KCSAbeywickrama/Function-Generator/Enclosure/Renderings/1000uF_16V.JPG

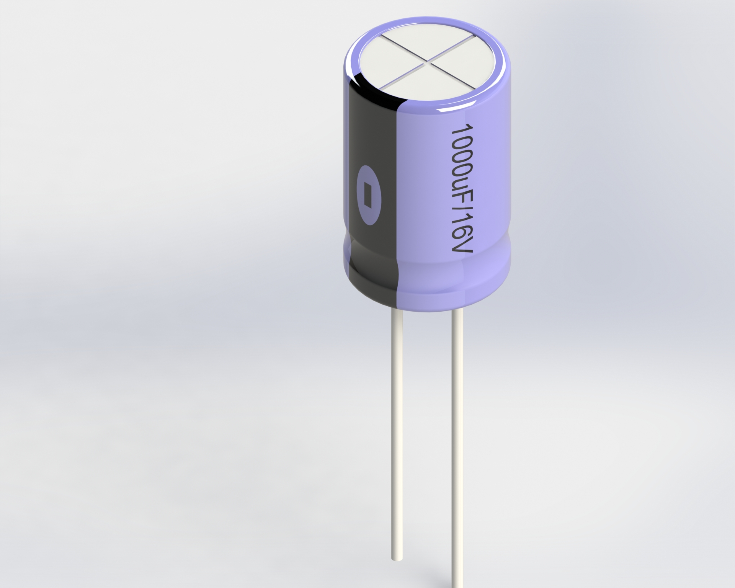
Enclosure/Renderings/1000uF_16V.JPG
