KCSAbeywickrama/Function-Generator/Enclosure/RV24AF-22-15R.png

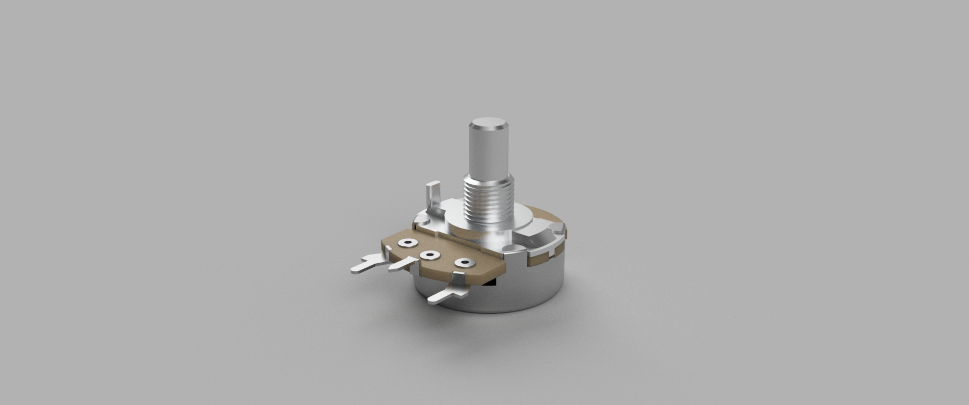
Enclosure/RV24AF-22-15R.png
