KCSAbeywickrama/Function-Generator/Enclosure/transformer/Transformer.step

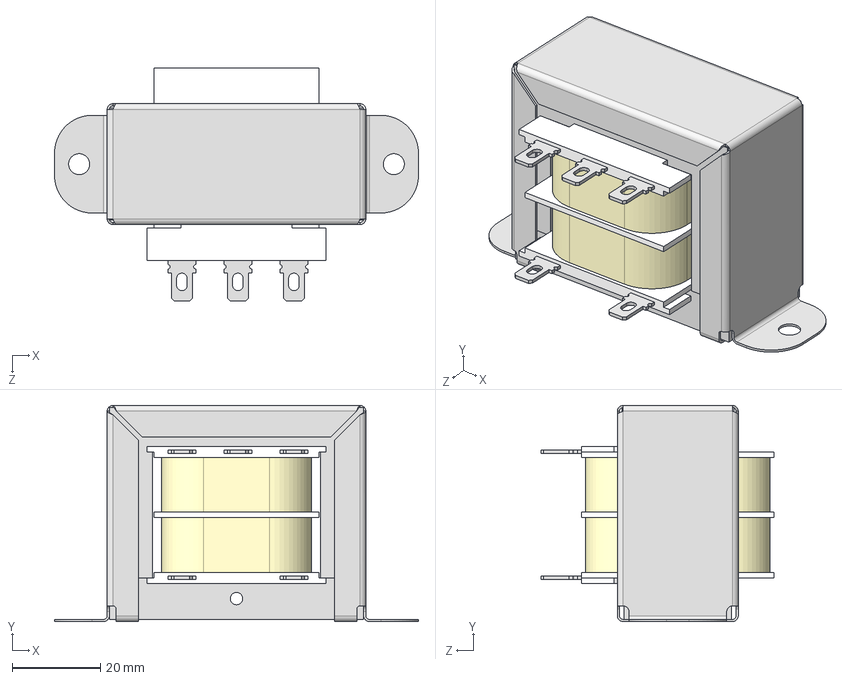
[picture p33: CAD file, 2022-11-06]
Enclosure/transformer/Transformer.step
82.6 x 49.0 x 52.9 mm
