KCSAbeywickrama/Function-Generator/Enclosure/spacer.SLDPRT

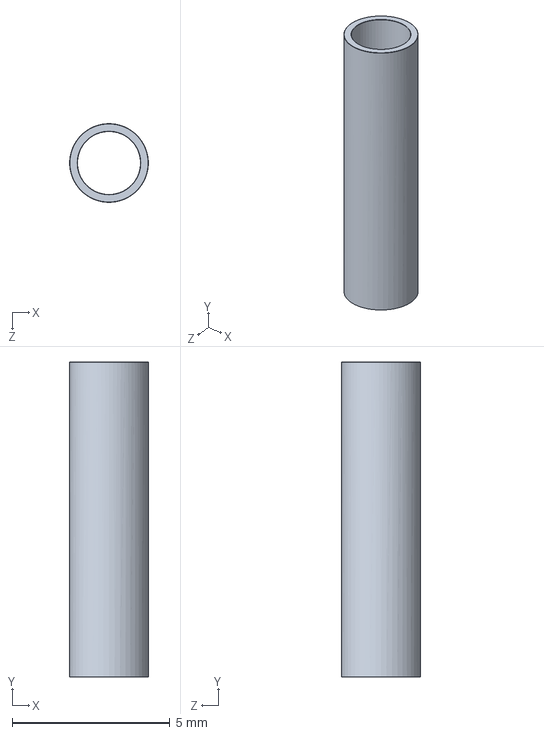
[picture p34: CAD file, 2022-11-06]
Enclosure/spacer.SLDPRT
2.50 x 10.0 x 2.50 mm
