KCSAbeywickrama/Function-Generator/Enclosure/probe_port.SLDPRT

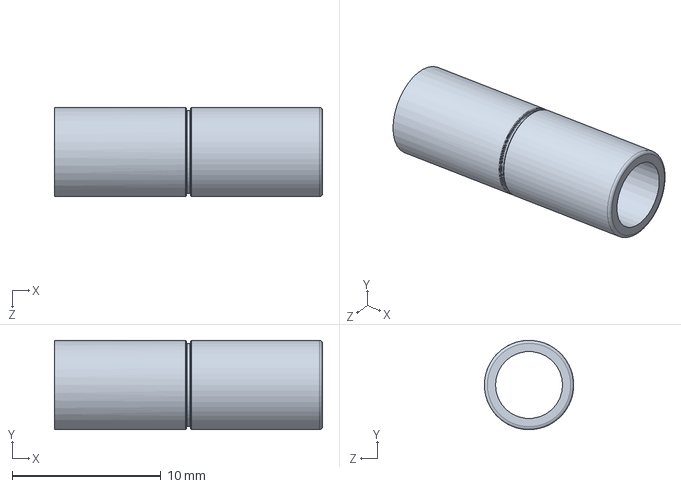
[picture p35: CAD file, 2022-11-06]
Enclosure/probe_port.SLDPRT
18.0 x 6.00 x 5.99 mm
