KCSAbeywickrama/Function-Generator/Enclosure/1000uF_16V.STEP

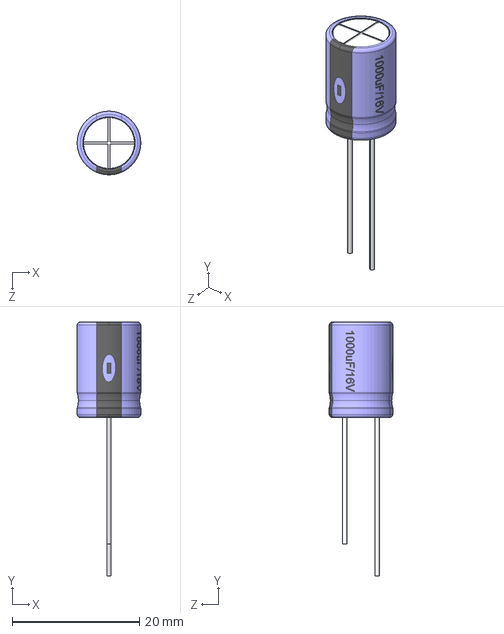
[picture p36: CAD file, 2022-11-06]
Enclosure/1000uF_16V.STEP
9.99 x 39.9 x 10.0 mm
