KCSAbeywickrama/Function-Generator/Enclosure/RV24AF-22-15R.step

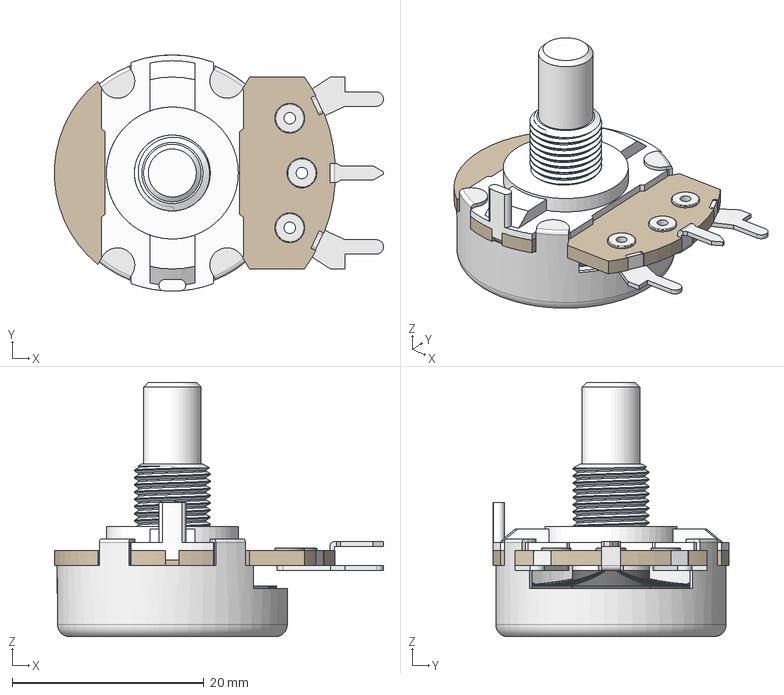
[picture p37: CAD file, 2022-11-06]
Enclosure/RV24AF-22-15R.step
34.3 x 24.6 x 26.5 mm
