KCSAbeywickrama/Function-Generator/Enclosure/knob_large.SLDPRT

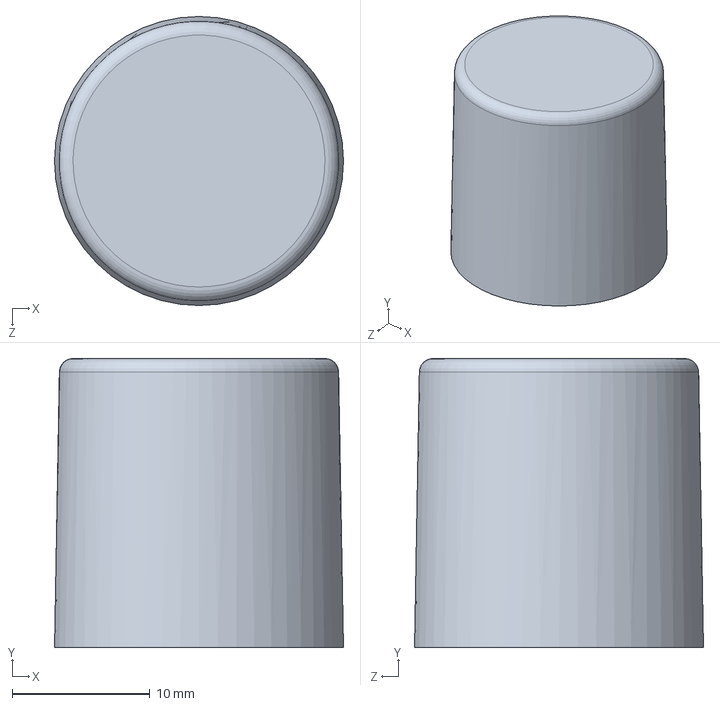
[picture p38: CAD file, 2022-11-06]
Enclosure/knob_large.SLDPRT
21.0 x 21.0 x 21.0 mm
