KCSAbeywickrama/Function-Generator/Enclosure/pwr_supply.SLDPRT

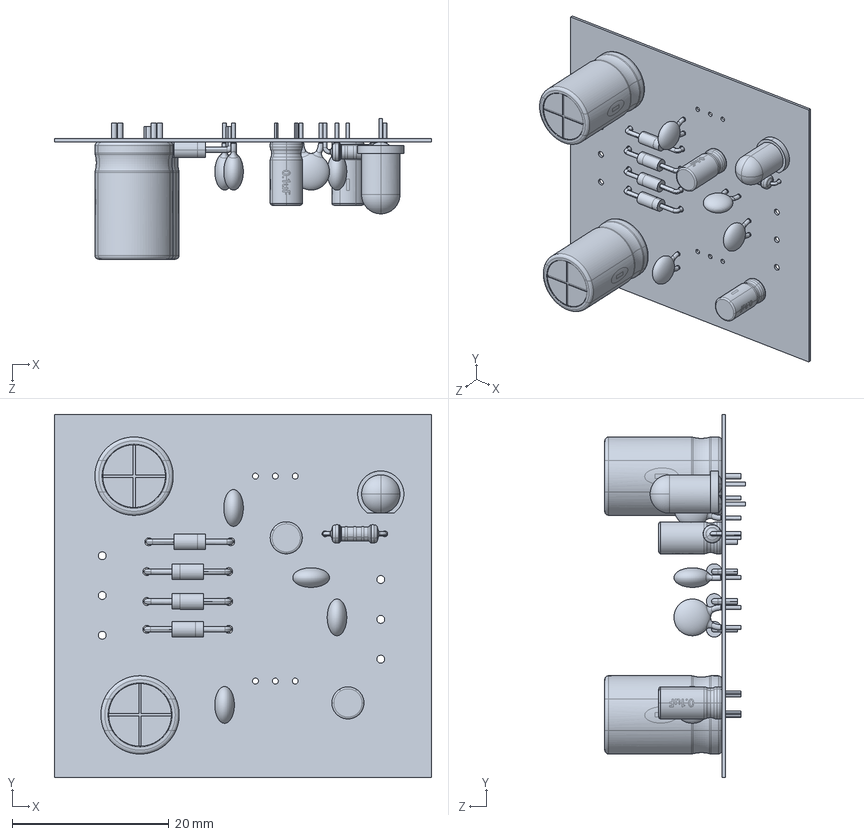
[picture p39: CAD file, 2022-11-06]
Enclosure/pwr_supply.SLDPRT
48.1 x 46.4 x 17.9 mm
