KCSAbeywickrama/Function-Generator/Enclosure/power switch.SLDPRT

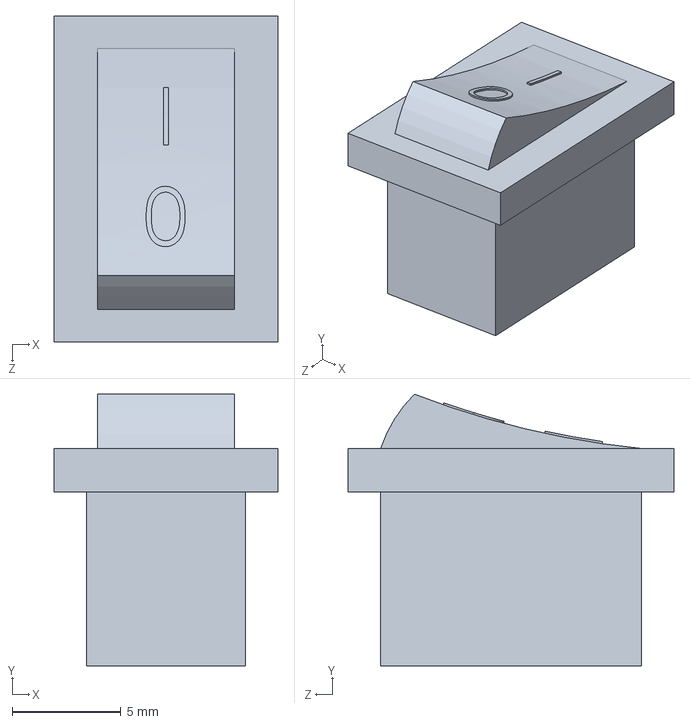
[picture p40: CAD file, 2022-11-06]
Enclosure/power switch.SLDPRT
10.3 x 12.5 x 15.0 mm
