KCSAbeywickrama/Function-Generator/PCB/Power_Supply_Project/PWR_supply_sch.step

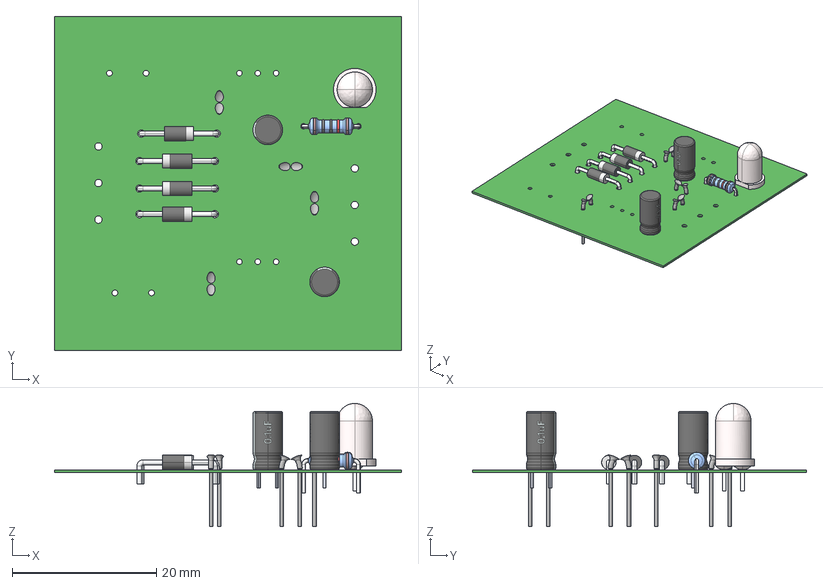
[picture p41: CAD file, 2022-11-06]
PCB/Power_Supply_Project/PWR_supply_sch.step
48.1 x 46.4 x 17.1 mm
Resistor_10K_Ohm_tol1pct_0,25W__07,62
0.1uF x 2
LED_5mm_white_TH
Diode_(1) x 4
10pF_Ceramic_Disc_2_RGB8421504 x 4
