KCSAbeywickrama/Function-Generator/Enclosure/POWER_SWITCH_1353.SLDPRT

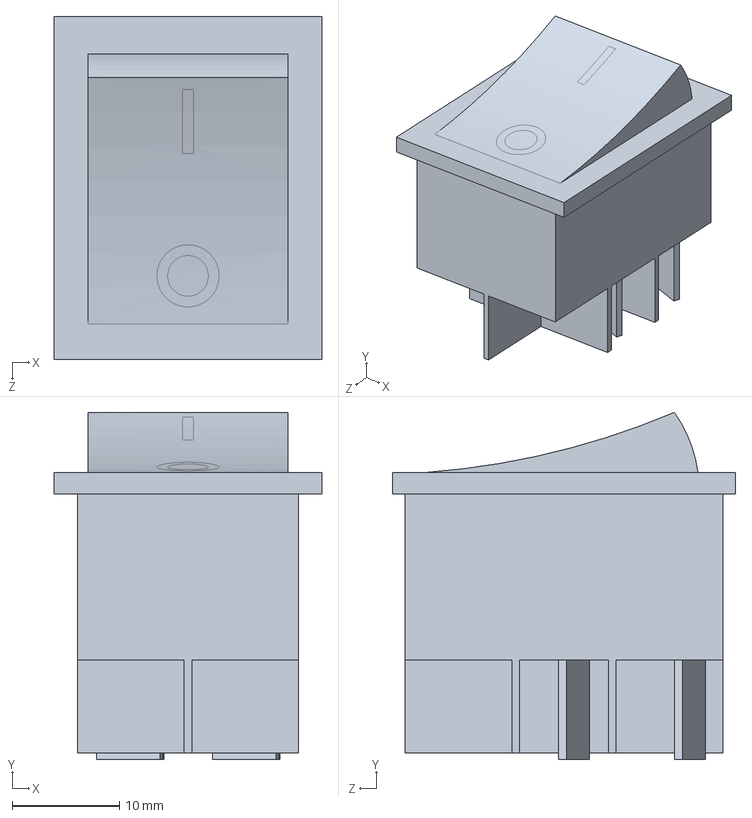
[picture p42: CAD file, 2022-11-06]
Enclosure/POWER_SWITCH_1353.SLDPRT
25.0 x 32.4 x 32.0 mm
