KCSAbeywickrama/Function-Generator/Enclosure/knob_small.SLDPRT

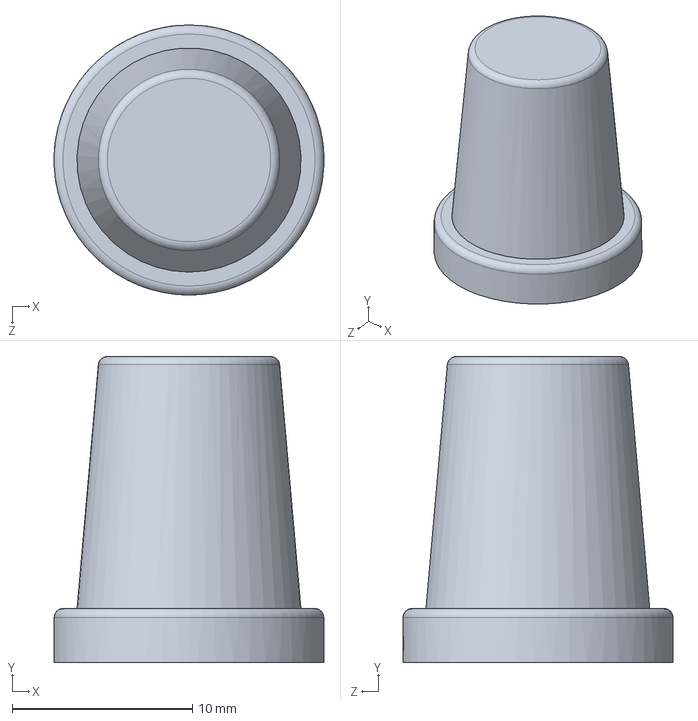
[picture p43: CAD file, 2022-11-06]
Enclosure/knob_small.SLDPRT
15.0 x 17.0 x 15.0 mm
