KCSAbeywickrama/Function-Generator/Prints/multisim.png

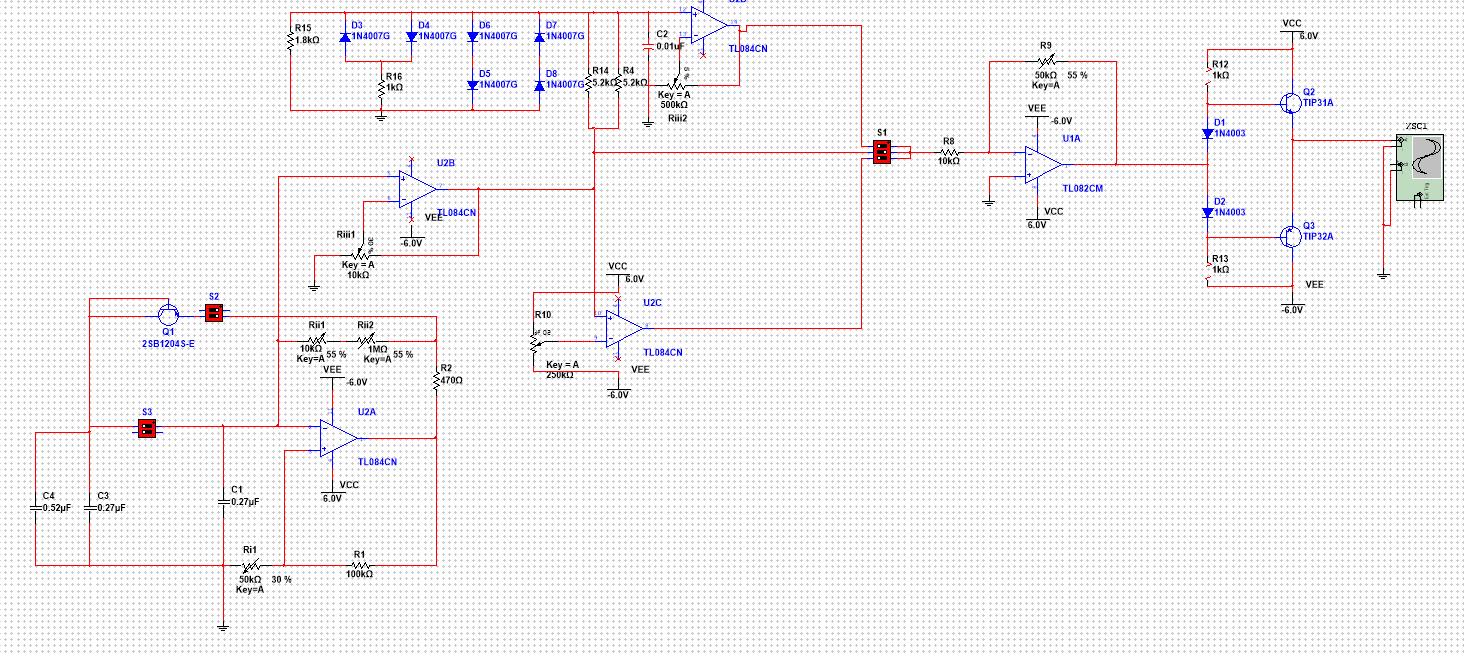
Prints/multisim.png
