KCSAbeywickrama/Function-Generator/PCB/Fucntion_Generator_Project/Prints/Top_G02_new.pdf

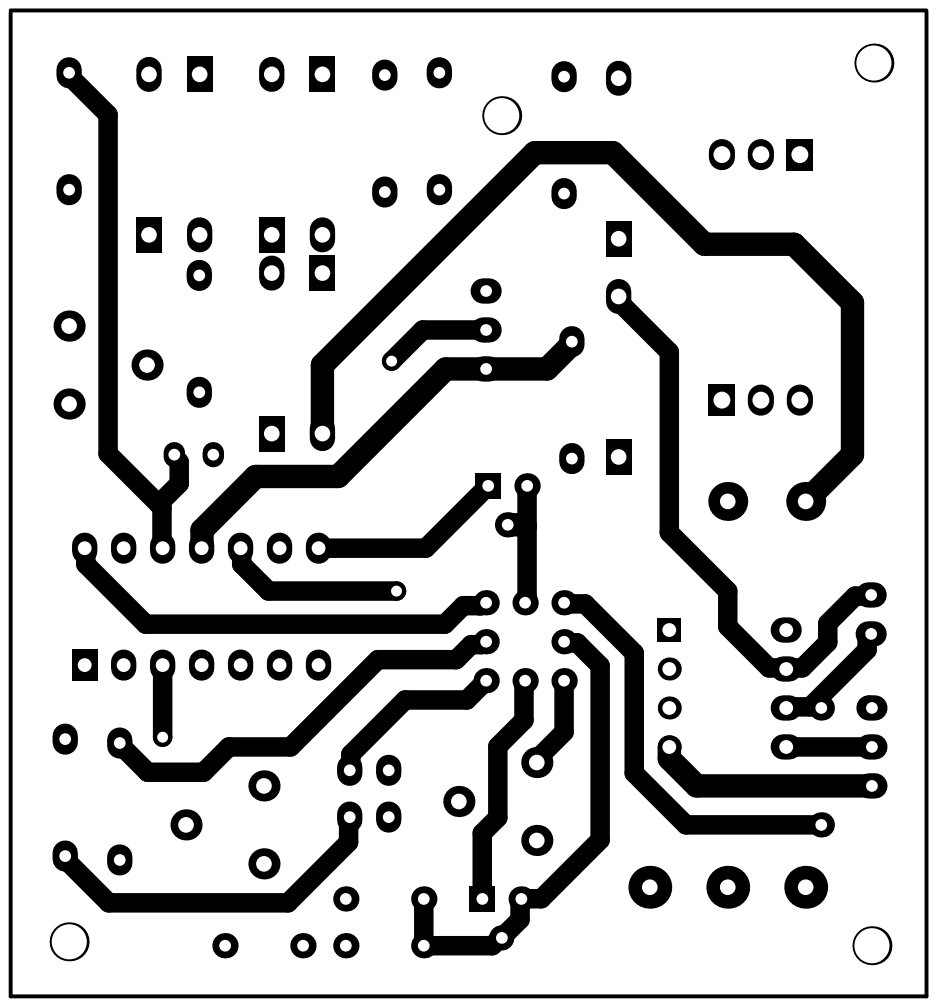
[picture p59: page 1]
